machadoleonardo94/smog-alado/Firmware_8266/smog-alado/src/components/ADS1115/docs/absolute_max_ratings.png

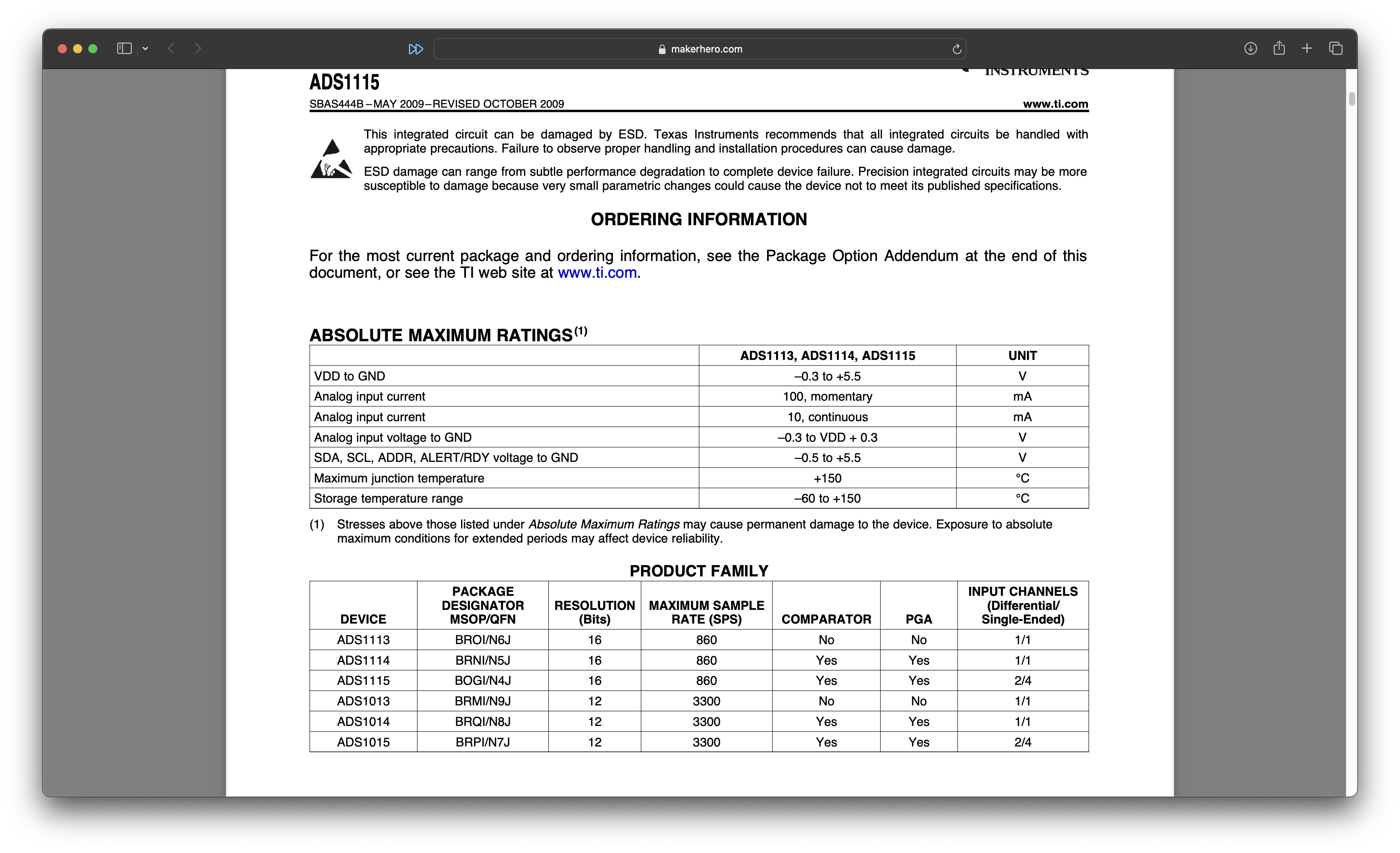
Firmware_8266/smog-alado/src/components/ADS1115/docs/absolute_max_ratings.png
