machadoleonardo94/smog-alado/Firmware_C3/src/components/ESP32/docs/MCP2561_abs.jpeg

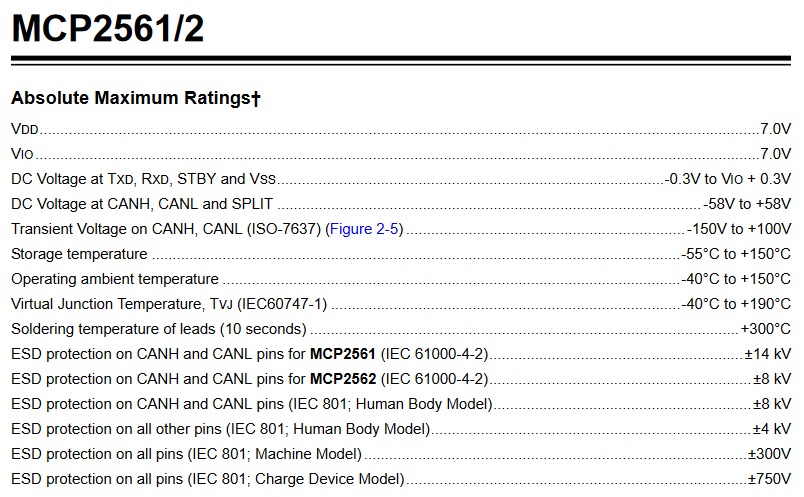
Firmware_C3/src/components/ESP32/docs/MCP2561_abs.jpeg
