machadoleonardo94/smog-alado/Firmware_C3/src/components/ESP32/docs/MCP2561_dc.jpeg

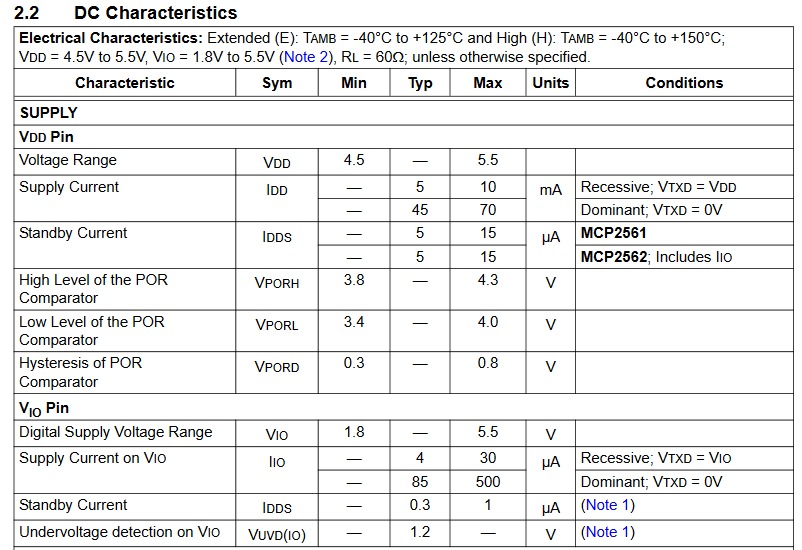
Firmware_C3/src/components/ESP32/docs/MCP2561_dc.jpeg
