machadoleonardo94/smog-alado/Firmware_8266/smog-alado/src/shared/interfaces.h

#if !defined(PROJECT_GLOBAL_INTERFACES)
#define PROJECT_GLOBAL_INTERFACES

//* ---------------------- I2C ----------------------
//* ADS1115 - default 0x48 - 4 channels 16 bits ADC.

//* ---------------------- UART ----------------------
//* Serial port used for USB connection to the PC.
#define serialMon Serial

#endif // PROJECT_GLOBAL_INTERFACES
